nagapi2357-ui/Prime_Maxel-v3/research/Pythagorean_PWT_Connections.md

# Pythagorean Lost Secrets & Prime Wave Torsion — Research Note

**Author:** Nagaπ (with Adrian / Tusk Innovations)
**Date:** 5 March 2026
**Source Material:** Ken L. Wheeler, "Pythagoras Lost Secrets Recovered" (Feb 2026)
**Context:** Connections to Prime Wave Torsion (PWT) research and the Prime_Maxel-v3 circuit

---

## 1. Summary of Wheeler's Framework

Ken Wheeler presents a reconstruction of the ancient Pythagorean "Divided Line" (Plato's Republic 509d–511), arguing it encodes the complete structure of the cosmos through powers of Φ (phi, the golden ratio = 1.618033…).

### Core Claims

**The Divided Line as Universal Template:**
A single line, divided in harmonic ratio, then each section divided again identically, produces four segments corresponding to:

| Segment | Greek Letter | Element | Value | Meaning |
|---|---|---|---|---|
| Ι (Iota) | The One | Light/Principle | 1 | The Absolute |
| Θ (Theta) | Logos | Fire/Illumination | Φ | Beauty, harmony, the "holographic One" |
| Α (Alpha) | Animus | Air/Breath/Life | 1 (midpoint) | Living soul, breath of existence |
| Υ (Upsilon) | Water | — | 1 | Mediator |
| Γ (Gamma) | Gaia | Earth/Matter | 1/Φ | Phenomena, material world |

These spell ΥΓΙΘΑ (Ugieia) — the untranslatable Pythagorean greeting implying harmony, perfection, divine order, wholeness, beauty, and symmetry.

**The Circle is Φ³:**
- 360° = 137.5° + 137.5° + 85°
- 137.5° = the golden angle (Φ expressed in angular measure)
- 85° = 1 (the unit)
- 85 × Φ = 137.5
- 360 ÷ 85 = Φ³ = 4.23606…
- Therefore: a circle = Φ + Φ + 1 = Φ³

**The 108-36-36° Triangle:**
The isosceles triangle with apex 108° and base angles 36° is the only perfectly incommensurable geometry — self-similar at every scale. An "incommensurable cut" produces an identical smaller triangle. This is the geometry of the water molecule and the building block of the pentagram.

**Powers of Phi as Ontological Hierarchy:**

| Power | Value | Domain |
|---|---|---|
| Φ⁻³ | 0.23606 | ἀγνωσία — agnosis, the aoristos-dyad, ananke |
| Φ⁻² | 0.38196 | ψυχή — psyche, atman, citta, nous |
| 1/Φ | 0.61803 | Matter, phenomena |
| 1 | 1.0 | Being, the midpoint |
| Φ | 1.61803 | Beauty, logos, harmony |
| Φ² | 2.61803 | κόσμος νοητός — the metaphysical universe |
| Φ³ | 4.23606 | ALL — Pan, the entire universe |

**The Four Elements as Intermediates:**
The ancient diagram of Ignis–Aer–Aqua–Terra (Fire–Air–Water–Earth) with their qualities (Calidus/Frigida, Siccus/Humida, Subtilis/Corpulenta, Mobilis/Immobilis) maps onto the divided line, with "inmediate" relationships at ratios 8:12:18:27 — a geometric progression.

### The Ouroboros-Pentagram-Tree

The final image (slide 11) shows the serpent (ouroboros) encircling the pentagram inscribed over the tree of life — the Naga at the boundary, containing and bridging all realms.

---

## 2. The Royal Cubit Derivation

Adrian's independent derivation shows:

```
1 Royal Cubit = 0.5236m (established 1925, from pyramid measurements)

π / 6 = 0.52360…
π - Φ² = 3.14159… - 2.61803… = 0.52356…  ≈ 0.5236

Therefore: The Cubit ≈ π - Φ²
```

Additional note: 5 × 2 × 3 × 6 = 180 = π radians.

**Significance:** The ancient unit of measurement encodes the *difference* between transcendence (π, the irrational circle) and golden self-similarity (Φ²). The cubit is literally the gap between two fundamental constants — a bridge quantity.

---

## 3. Connections to Prime Number Theory

### 3.1 Φ and Primes — The Structural Bond

The Fibonacci sequence F(n), whose consecutive ratios converge to Φ, has deep prime entanglement:

- **Divisibility:** Every prime p divides some Fibonacci number. Specifically, p | F(p−1) or p | F(p+1) (depending on p mod 5).
- **Fibonacci primes:** F(n) is prime only if n is prime (necessary but not sufficient) — primality is a prerequisite for Fibonacci primality.
- **Lucas primality tests:** Lucas sequences (built on Φ) are the basis of the Lucas-Lehmer test for Mersenne primes, one of the most powerful primality tests known.
- **Zeckendorf's theorem:** Every positive integer has a unique representation as a sum of non-consecutive Fibonacci numbers — an alternative "base-Φ" decomposition paralleling prime factorisation.

Wheeler's framework suggests Φ is not merely a ratio but the *generative principle* of manifestation. If so, primes — as the irreducible atoms of arithmetic — would naturally emerge from Φ-structured processes.

### 3.2 The 108-36-36° Triangle and Self-Similar Prime Distribution

The incommensurable triangle's defining property is **fractal self-similarity**: subdivide it and the part is identical to the whole. Prime distribution exhibits analogous behaviour:

- **Scaling invariance:** The prime counting function π(x) ~ x/ln(x) shows that primes "thin out" logarithmically, but the *local* distribution at any scale resembles the global pattern — Cramér's model treats prime gaps as locally random with globally predictable statistics.
- **The Ulam spiral:** Primes plotted on a square spiral cluster along diagonal lines (quadratic polynomials). This is an empirical self-similarity — the pattern at small scale echoes at large scale.
- **Benford's law for primes:** The distribution of leading digits of primes follows logarithmic patterns reminiscent of golden-ratio scaling.

The 108-36-36° triangle may offer a geometric language for describing this: primes as the "incommensurable cuts" of the number line, each one producing a smaller copy of the overall distribution pattern.

### 3.3 The Golden Angle (137.5°) and Prime Spirals

The golden angle — 360° × (1 - 1/Φ) = 137.5077…° — is nature's optimal packing angle (sunflower seeds, phyllotaxis, sand dollars).

**Prime spiral hypothesis:** If primes are plotted on a spiral where each successive integer advances by the golden angle (rather than equal angular steps as in Ulam's spiral), do new patterns emerge? The golden angle's irrationality guarantees maximal separation between successive points, which could reveal prime clustering patterns invisible in Cartesian or equal-angle representations.

This connects directly to our PCB: the 12 Golden Cells at 30° spacing approximate a dodecagonal symmetry — but a golden-angle spacing (137.5° between successive cells) would create a phyllotactic arrangement, potentially more aligned with the theory.

### 3.4 Powers of Phi and Prime Gap Distribution

Wheeler's hierarchy (Φ⁻³ through Φ³) suggests discrete "levels" of manifestation. Prime gaps show a suggestive structure:

- The average gap near prime p is ~ln(p)
- The *distribution* of gap sizes follows patterns related to the Hardy-Littlewood conjectures
- **Observation:** The ratio of successive "record" prime gaps approximates Φ in certain ranges — e.g., the jump from gap 6 to gap 8 to gap 14 to gap 20 to gap 34… the Fibonacci-like growth pattern in maximal gaps has been noted by multiple researchers

If prime gaps grow in a Φ-scaled hierarchy, Wheeler's ontological levels would map to gap-size classes, with each "level" containing primes of a particular density character.

### 3.5 Five as the Generative Prime

Wheeler places 5 at the centre: Being = 5. In number theory, 5 is uniquely significant:

- **5 = Φ² + Φ⁻²** — the sum of golden powers
- **√5** appears in Binet's formula for Fibonacci numbers: F(n) = (Φⁿ - ψⁿ)/√5
- **5** is the hypotenuse-squared of the smallest Pythagorean triple (3² + 4² = 5²)
- **5** is the smallest prime that is a sum of two primes (2 + 3)
- **mod 5** determines Fibonacci divisibility by primes (via the Legendre symbol)
- The **pentagram** (5-pointed star) encodes Φ in every proportion
- **Fermat prime:** 5 = 2^(2¹) + 1, the second Fermat prime

In our circuit, the 12 cells × 5 signals per cell (TORSION_A, TORSION_B, VREF_MID, PULSE_IN, I2C) = 60 signal connections, and 60 = 5 × 12 = the number of edges in an icosahedron.

---

## 4. Dimensional Relationships

### 4.1 One-Dimensional: The Divided Line

The number line itself is Wheeler's Divided Line. Primes are the "uneven divisions" that create the harmonic structure:

- The fundamental theorem of arithmetic (unique prime factorisation) means every integer is a multiplicative "emanation" from primes — exactly Wheeler's claim that everything is a "multiplicative iteration of the One."
- The Sieve of Eratosthenes is literally the process of making successive cuts — each prime "divides" the line into harmonics.

### 4.2 Two-Dimensional: Spirals and Rings

**Ulam Spiral:** Primes on a square spiral → diagonal patterns (Hardy-Littlewood conjecture).

**Sacks Spiral:** Primes on an Archimedean spiral → parabolic curves.

**Golden Spiral:** Primes on a Φ-spiral → *unexplored territory*. The golden spiral's self-similar growth rate may resonate with the self-similar distribution of primes.

**Gaussian Primes:** In the complex plane Z[i], primes split into patterns governed by their residue mod 4:
- p ≡ 1 (mod 4) → splits into two Gaussian primes (e.g., 5 = (2+i)(2−i))
- p ≡ 3 (mod 4) → remains prime in Z[i]
- 2 = −i(1+i)² — the unique ramified prime

This 2D structure creates a lattice where prime distribution has *geometric* character — some primes are "larger" (unsplit) and others fragment into conjugate pairs, creating a torsion-like pairing.

**Our PCB's concentric rings** on B.Cu are a physical 2D prime-inspired geometry: TORSION_A (outer ring) and TORSION_B (inner ring) create paired concentric paths — a materialised Gaussian prime structure where signals flow in conjugate pairs.

### 4.3 Three-Dimensional: Zeta Landscape and Platonic Solids

**The Riemann Zeta Function |ζ(s)|:**
Plotted over the complex plane, the zeta function creates a 3D landscape of peaks and valleys. The non-trivial zeros — all conjectured to lie on the critical line Re(s) = ½ — are the "divided line" of analytic number theory. This ½ is Wheeler's midpoint (Alpha/Being), and the zeros encode the exact positions of primes.

**Platonic Solids and Phi:**
The icosahedron (20 triangular faces) and dodecahedron (12 pentagonal faces) are the only Platonic solids whose geometry is defined by Φ. Their vertices sit at coordinates involving (0, ±1, ±Φ) and permutations.

- The dodecahedron has **12 faces** — matching our 12 Golden Cells
- Each face is a **pentagon** — the Pythagorean ΥΓΙΘΑ symbol
- The dihedral angle of the dodecahedron is **116.565°** ≈ 360° - 2 × 137.5° (complement of two golden angles minus 360° ≈ 85° = Wheeler's "1")

**Quaternionic Primes (4D):**
In the Hurwitz quaternions, primes extend to 4 dimensions. The 24-cell polytope — unique to 4D and self-dual — governs the unit quaternions. It has 24 vertices, 96 edges, and 24 octahedral cells. Its structure intersects with the golden ratio through the 600-cell (which has icosahedral symmetry).

### 4.4 The Torsion Bridge as Dimensional Probe

Our circuit's TORSION_A and TORSION_B form a **differential pair** — mathematically, a 1D projection of a 2D phenomenon (the difference between two signals). By arranging 12 such pairs radially, we create:

- **1D:** Each differential measurement (TORSION_A − TORSION_B) per cell
- **2D:** The radial array of 12 measurements → angular distribution, like reading the "spiral" at 12 points
- **3D:** If cells are driven with phase-shifted excitations, the time dimension creates a helical (screw/torsion) pattern in signal space

This maps directly onto Wheeler's hierarchy: the One (total signal) → Logos (the differential) → Life (the dynamic/time-varying) → Water (the flowing/propagating) → Earth (the physical copper trace).

---

## 5. The Cubit as Torsion Constant

The Royal Cubit = π − Φ² deserves special attention.

In our context, "torsion" is the differential tension between two states. The cubit is precisely this — the *tension* between the two most fundamental mathematical constants:

- **π** = the circle, rotation, cycles, waves — the electromagnetic
- **Φ²** = self-similar growth, recursion, scaling — the structural/arithmetic

Their difference (0.5236) is small relative to either (~17% of π, ~20% of Φ²), suggesting the two principles are *almost* reconciled but not quite — there is a residual torsion. This residual is what the ancients encoded in their unit of measurement.

**Speculative connection:** If prime distribution is governed by the interplay of cyclic phenomena (the "music of the primes" in zeta function language) and self-similar scaling (the logarithmic thinning), then the "torsion" between these two principles — quantified by π − Φ² — may appear as a fundamental constant in prime gap statistics.

To test: examine whether π − Φ² (≈ 0.5236) or its reciprocal (≈ 1.9099) appears in the statistical distribution of normalized prime gaps.

---

## 6. The Naga Connection

The ouroboros serpent (slide 11) encircling the pentagram is the Naga — the bridge entity at the boundary between realms. In Adrian's mythology (Dusty's Road), Naga is "one of humanity's oldest words — found at water's edge on the deepest archaeological artefacts."

Wheeler places Water (Υ/Upsilon) as the mediator between Logos and Earth on the divided line. The Naga sits precisely here — at the water's edge, mediating between the intelligible and the sensible, between the abstract pattern (primes) and the physical measurement (circuit).

Our instrument is, in this framing, a Naga device: it sits at the interface between mathematical structure (the prime-inspired topology) and physical signal (the electromagnetic measurement), seeking to detect the torsion between worlds.

---

## 7. Open Questions for Future Investigation

1. **Golden-angle prime spiral:** Plot primes on a 137.5° spiral — do new clustering patterns emerge beyond Ulam/Sacks?
2. **Φ-scaled prime gaps:** Do maximal prime gaps grow as a Fibonacci-like sequence? Formalise the observation.
3. **π − Φ² in prime statistics:** Search for this constant in normalised prime gap distributions, twin prime ratios, or zeta zero spacings.
4. **Dodecahedral cell arrangement:** Would 12 cells at golden-angle spacing (rather than 30° equal spacing) produce different torsion signatures?
5. **5-fold signal symmetry:** The 5 signals per cell (TORSION_A/B, VREF, PULSE, I2C) — is there a natural pentagrammatic organisation of their relationships?
6. **Wildberger's maxel algebra:** Apply the maxel trend index framework (from the Symbiotic Futures project) to model prime-to-prime "ping" propagation through multiplicative structure.
7. **3D extension:** Design a follow-up board with cells arranged on a spherical or helical topology, probing 3D torsion.

---

## References

- Wheeler, K.L. (2026). "Pythagoras Lost Secrets Recovered." YouTube. https://youtu.be/AeIJzEDdEjI
- Plato, *Republic*, 509d–511e (The Divided Line)
- *Theology of Arithmetic* (attributed to Iamblichus)
- Timaeus, 31b–32c ("Two things alone cannot be satisfactorily united without a third")
- Wildberger, N.J. — Maxel algebra framework (rational trigonometry / algebraic number theory)
- Hardy, G.H. & Littlewood, J.E. — Conjectures on prime distributions
- Riemann, B. — "On the Number of Primes Less Than a Given Magnitude" (1859)

---

*"The (power of the) Divine's Illumination hath breathed life into the Waters & Firmament."*
*— ΥΓΙΘΑ, the Pythagorean greeting*
