nagapi2357-ui/Prime_Maxel-v3/research/emf_spectrum_patterns.md

# Electromagnetic Spectrum, Human Senses & Mathematical Patterns

*Research compiled 2026-04-05*

---

## 1. The 7 Colours of Visible Light

Using c = λf where c ≈ 2.998 × 10⁸ m/s:

| Colour  | Wavelength (nm) | Frequency (THz) | Frequency (Hz) |
|---|---|---|---|
| Red | 620–750 | 400–484 | 4.00 × 10¹⁴ – 4.84 × 10¹⁴ |
| Orange  | 590–620 | 484–508 | 4.84 × 10¹⁴ – 5.08 × 10¹⁴ |
| Yellow  | 565–590 | 508–530 | 5.08 × 10¹⁴ – 5.30 × 10¹⁴ |
| Green | 500–565 | 530–600 | 5.30 × 10¹⁴ – 6.00 × 10¹⁴ |
| Blue | 450–500 | 600–666 | 6.00 × 10¹⁴ – 6.66 × 10¹⁴ |
| Indigo  | 420–450 | 666–714 | 6.66 × 10¹⁴ – 7.14 × 10¹⁴ |
| Violet  | 380–420 | 714–789 | 7.14 × 10¹⁴ – 7.89 × 10¹⁴ |

**Key observation:** The full visible range spans ~400 THz to ~789 THz.
Ratio: 789/400 ≈ **1.97:1** — almost exactly **one octave** (2:1).

### Centre Frequencies (geometric mean of each band)

| Colour  | Centre freq (THz) | Normalised (Red=1.000) |
|---|---|---|
| Red | 440 | 1.000 |
| Orange  | 496 | 1.127 |
| Yellow  | 519 | 1.180 |
| Green | 564 | 1.282 |
| Blue | 632 | 1.436 |
| Indigo  | 689 | 1.566 |
| Violet  | 750 | 1.705 |

---

## 2. The 7 Notes of a Musical Scale (One Octave)

### Equal Temperament (A4 = 440 Hz, showing C major scale)

| Note | Frequency (Hz) | Ratio to C4 | Interval |
|---|---|---|---|
| C4 | 261.63 | 1.000 | Unison |
| D4 | 293.66 | 1.122 | Major 2nd |
| E4 | 329.63 | 1.260 | Major 3rd |
| F4 | 349.23 | 1.335 | Perfect 4th |
| G4 | 392.00 | 1.498 | Perfect 5th |
| A4 | 440.00 | 1.682 | Major 6th |
| B4 | 493.88 | 1.888 | Major 7th |
| C5 | 523.25 | 2.000 | Octave |

### Just Intonation Ratios (for comparison)

| Note | Ratio | As fraction | Prime factors |
|---|---|---|---|
| C | 1.000 | 1/1 | — |
| D | 1.125 | 9/8 | 3²/2³ |
| E | 1.250 | 5/4 | 5/2² |
| F | 1.333 | 4/3 | 2²/3 |
| G | 1.500 | 3/2 | 3/2 |
| A | 1.667 | 5/3 | 5/3 |
| B | 1.875 | 15/8 | (3×5)/2³ |
| C' | 2.000 | 2/1 | 2 |

**Note:** Just intonation intervals are built entirely from primes **2, 3, and 5** — the first three primes. This is the foundation of harmonic consonance.

---

## 3. The Five Human Senses and Their Spectral Domains

### 3.1 Sight — Electromagnetic Radiation
- **Range:** ~380–750 nm (400–789 THz)
- **Detector:** Retinal photoreceptors (rods, 3 types of cones)
- **Mechanism:** Photon absorption → cis-trans isomerisation of retinal
- **Bandwidth:** ~1 octave of EM spectrum

### 3.2 Hearing — Mechanical Pressure Waves
- **Range:** ~20 Hz – 20 kHz (acoustic, not EM)
- **Detector:** Cochlear hair cells (tonotopically arranged)
- **Mechanism:** Basilar membrane resonance → mechanotransduction
- **Bandwidth:** ~10 octaves (2¹⁰ ≈ 1000:1 ratio)
- **Note:** Sound is NOT electromagnetic — it's longitudinal pressure waves in matter

### 3.3 Touch — Mechanical Pressure + Thermal (IR)
- **Pressure:** DC to ~1 kHz vibrotactile
- **Thermal:** Skin responds to IR radiation (~3–50 μm, peak sensitivity ~10 μm = 30 THz)
- **Detectors:** Meissner (light touch), Pacinian (vibration), Ruffini (stretch), Merkel (pressure), free nerve endings (pain/temp)
- **Thermal note:** We literally feel infrared radiation — hold hand near a hot object without touching it

### 3.4 Smell — Molecular Shape + Vibration
- **Traditional model:** Lock-and-key (molecular shape fits receptor)
- **Vibrational theory (Luca Turin):** Olfactory receptors may detect molecular vibration frequencies via inelastic electron tunnelling
  - If true, smell operates in the **IR range** (~1–100 THz, wavenumbers ~33–3333 cm⁻¹)
  - This would make smell a kind of **biological spectroscopy**
- **Frequency range of molecular vibrations:** ~10¹² – 10¹⁴ Hz (THz to low-IR)
- **Status:** Controversial but not disproven. Some evidence shows humans can distinguish isotopes (same shape, different vibration)

### 3.5 Taste — Chemical/Electrical
- **Modalities:** Sweet, sour, salty, bitter, umami (+ fat, possibly more)
- **Mechanism:** Chemical binding to G-protein coupled receptors (sweet/bitter/umami) or ion channels (sour/salty)
- **Not directly frequency-based** — operates on molecular recognition
- **Indirect EM connection:** Molecular binding involves electron orbital interactions at optical/UV frequencies

### Summary Table

| Sense | Physical domain | Frequency range | Octaves  | EM? |
|---|---|---|---|-----|
| Sight | EM radiation | 400–789 THz | ~1 | Yes |
| Hearing | Pressure waves | 20 Hz – 20 kHz | ~10 | No  |
| Touch | Pressure + thermal  | DC–1kHz + 3–100 THz | mixed | Partial |
| Smell | Molecular vibration | ~1–100 THz (if Turin)  | ~7 | Indirect |
| Taste | Chemical binding | N/A (not frequency-based)| — | No  |

---

## 4. Key Analysis: Colour-Music Correspondence

### 4.1 Visible Light Ratios vs Musical Intervals

Mapping the 7 colour centre frequencies as ratios from red:

| Colour  | Ratio from Red | Nearest musical interval | Just ratio | Match? |
|---|---|---|---|---|
| Red | 1.000 | Unison (C) | 1.000 | ✓ |
| Orange  | 1.127 | Major 2nd (D) | 1.125 | **≈ YES** (0.2% off) |
| Yellow  | 1.180 | Minor 3rd? | 1.200 | ~close |
| Green | 1.282 | Major 3rd (E) | 1.250 | ~2.5% off |
| Blue | 1.436 | Perfect 4th? (F) | 1.333 | ✗ off by 8% |
| Indigo  | 1.566 | Perfect 5th? (G) | 1.500 | ~4% off |
| Violet  | 1.705 | Major 6th? (A) | 1.667 | ~2% off |

**Verdict:** The match is **suggestive but imprecise**. Red→Orange maps beautifully to a major second. Green approximates a major third. But the middle and upper colours deviate significantly from clean musical intervals.

### 4.2 Newton's Colour-Music Mapping — Genius or Forced?

Newton explicitly mapped his 7 colours to the 7 notes of the Dorian mode:

| Newton's colour | Newton's note |
|---|---|
| Red | D |
| Orange | E |
| Yellow | F |
| Green | G |
| Blue | A |
| Indigo | B |
| Violet | C |

**Historical context:**
- Newton originally saw **5** colours in the spectrum (like most people)
- He **added** orange and indigo specifically to make 7, to match the musical scale
- He was deeply influenced by Pythagorean mysticism and the idea of cosmic harmony
- The choice of 7 was **partly forced** by his desire for musical correspondence

**However:**
- The fact that visible light spans almost exactly one octave is **NOT something Newton forced** — it's a physical fact about human photoreceptor sensitivity
- Newton's intuition that frequency ratios matter was **correct in principle**
- The specific colour-note mapping doesn't hold up to precise measurement

**Assessment: Newton was ~60% right.** The octave structure is real. The detailed mapping is forced.

### 4.3 The Visible Octave — Coincidence?

**The fact:** Human vision spans 400–789 THz ≈ 1.97:1 ≈ one octave.

**Arguments it's NOT coincidence:**
1. Three cone types (S, M, L) have peak sensitivities at ~420, ~530, ~560 nm
2. The ~2:1 ratio may relate to photochemistry constraints — the energy to break/isomerise retinal sets the lower bound, and UV damage sets the upper bound
3. Evolution may have "tuned" to one octave because it provides maximum information with minimum bandwidth
4. Water absorption: water is transparent in exactly this range, creating an evolutionary pressure window

**Arguments it IS coincidence:**
1. The boundaries are somewhat arbitrary (sensitivity trails off gradually)
2. Different definitions of "visible" give ratios from 1.7 to 2.1
3. Many animals see outside this range (bees see UV, snakes see IR)

**Best assessment:** It's a **constrained coincidence**. Physics (water transparency window, solar spectrum peak, photochemistry) constrains the range, and one octave happens to be about the right bandwidth for useful colour discrimination. The 2:1 ratio is approximate, not exact.

---

## 5. EM Spectrum Band Boundaries and Ratio Analysis

### 5.1 Standard EM Band Boundaries

| Band | Lower freq (Hz)  | Upper freq (Hz)  | Lower λ | Upper λ |
|---|---|---|---|---|
| ELF | 3 × 10⁰ | 3 × 10¹ | 10⁸ m | 10⁷ m |
| SLF | 3 × 10¹ | 3 × 10² | 10⁷ m | 10⁶ m |
| ULF | 3 × 10² | 3 × 10³ | 10⁶ m | 10⁵ m |
| VLF | 3 × 10³ | 3 × 10⁴ | 10⁵ m | 10⁴ m |
| LF | 3 × 10⁴ | 3 × 10⁵ | 10⁴ m | 10³ m |
| MF | 3 × 10⁵ | 3 × 10⁶ | 10³ m | 10² m |
| HF | 3 × 10⁶ | 3 × 10⁷ | 10² m | 10¹ m |
| VHF | 3 × 10⁷ | 3 × 10⁸ | 10 m | 1 m |
| UHF | 3 × 10⁸ | 3 × 10⁹ | 1 m | 0.1 m |
| SHF | 3 × 10⁹ | 3 × 10¹⁰ | 0.1 m | 0.01 m |
| EHF | 3 × 10¹⁰ | 3 × 10¹¹ | 10 mm | 1 mm |
| **Infrared** | 3 × 10¹¹ | 4 × 10¹⁴ | 1 mm | 750 nm |
| **Visible**  | 4 × 10¹⁴ | 7.89 × 10¹⁴ | 750 nm | 380 nm |
| **UV** | 7.89 × 10¹⁴ | 3 × 10¹⁶ | 380 nm | 10 nm |
| **X-ray** | 3 × 10¹⁶ | 3 × 10¹⁹ | 10 nm | 0.01 nm |
| **Gamma** | >3 × 10¹⁹ | — | <0.01 nm | — |

### 5.2 Major Band Ratios (using conventional boundaries)

Looking at the **major** EM regions:

| Transition | Lower (Hz) | Upper (Hz) | Ratio (upper/lower) | As power of 10 | Octaves |
|---|---|---|---|---|---|
| Radio → Microwave | 3×10⁴ | 3×10⁹ | 10⁵ | 5 | ~17 |
| Microwave → IR | 3×10⁹ | 3×10¹¹ | 10² | 2 | ~6.6 |
| IR → Visible | 3×10¹¹ | 4×10¹⁴ | ~1333 | 3.1 | ~10.4 |
| Visible → UV | 4×10¹⁴ | 7.89×10¹⁴ | ~1.97 | 0.3 | ~1 |
| UV → X-ray | 7.89×10¹⁴ | 3×10¹⁶ | ~38 | 1.6 | ~5.2 |
| X-ray → Gamma | 3×10¹⁶ | 3×10¹⁹ | 10³ | 3 | ~10 |

### 5.3 Ratio Analysis — Are There Patterns?

**Observation 1: Radio sub-bands are uniform decades (×10)**

Each radio sub-band (ELF→SLF→ULF→VLF→LF→MF→HF→VHF→UHF→SHF→EHF) spans exactly **one decade** (ratio 10:1 = ~3.32 octaves). This is purely a human convention (ITU designation), not physics.

**Observation 2: The physically meaningful bands have irregular ratios**

The transitions between IR, visible, UV, X-ray, and gamma are set by **physical processes**, not convention:
- IR/visible boundary: photoreceptor chemistry
- UV/X-ray boundary: atomic ionisation energies
- X-ray/gamma boundary: nuclear energy scales

These don't follow neat decimal or musical ratios.

**Observation 3: Powers of 10 dominate, but...**

The full EM spectrum from radio (10³ Hz) to gamma (10²⁰ Hz) spans ~17 decades. The major boundaries fall roughly at:

```
Radio:      10³  – 10⁹   Hz  (6 decades)
Microwave:  10⁹  – 10¹¹  Hz  (2 decades) 
IR:         10¹¹ – 10¹⁴  Hz  (3 decades)
Visible:    10¹⁴·⁶ – 10¹⁴·⁹ Hz (0.3 decades)
UV:         10¹⁴·⁹ – 10¹⁶·⁵ Hz (1.6 decades)
X-ray:      10¹⁶·⁵ – 10¹⁹·⁵ Hz (3 decades)
Gamma:      >10¹⁹·⁵ Hz
```

Decade widths: **6, 2, 3, 0.3, 1.6, 3, ...**

These don't obviously map to prime sequences, musical ratios, or clean mathematical patterns. The widths correlate with **how many distinct physical mechanisms operate** in each range.

### 5.4 Prime Structure in the Spectrum?

Looking at this differently — the **physically significant frequencies** in nature:

| Phenomenon | Frequency (Hz)  | Notable factor |
|---|---|---|
| Earth Schumann resonance | 7.83 | ≈ π × 2.49 |
| Human alpha brain waves | 8–13 | ~Schumann overlap |
| Human hearing limit | 2 × 10⁴ | 2⁴ × 5⁴ |
| Molecular rotation (gas) | ~10⁹ – 10¹¹ | — |
| Molecular vibration | ~10¹² – 10¹⁴ | — |
| Visible light (red edge) | 4 × 10¹⁴ | 2² × 10¹⁴ |
| Visible light (violet edge)  | 7.89 × 10¹⁴ | ≈ 8 × 10¹⁴ = 2³ × 10¹⁴ |
| Hydrogen 21-cm line | 1.42 × 10⁹ | — |
| Hydrogen Lyman-alpha | 2.47 × 10¹⁵ | — |

**The visible range in pure factors:**
- Red edge: ~4 × 10¹⁴ = 2² × 2¹⁴ × 5¹⁴ = 2¹⁶ × 5¹⁴ (in Hz with 10¹⁴ expanded)
- Violet edge: ~8 × 10¹⁴ = 2³ × 10¹⁴ = 2¹⁷ × 5¹⁴
- Ratio: 2¹⁷/2¹⁶ = **2** — one octave, expressed as a single power of the first prime

This is elegant: **the visible spectrum spans exactly one factor of 2 (the first prime)**.

---

## 6. The Gap Between Sound and Light

### 6.1 What Fills the Gap?

| Frequency range | Hz | What it is | Human perception? |
|---|---|---|---|
| 20 Hz – 20 kHz | 2×10¹ – 2×10⁴ | **Sound** (audible) | Hearing ✓ |
| 20 kHz – 1 GHz | 2×10⁴ – 10⁹ | Ultrasound → Radio waves | None directly |
| 1 GHz – 300 GHz | 10⁹ – 3×10¹¹ | **Microwaves** | None (but heats tissue)|
| 300 GHz – 430 THz | 3×10¹¹ – 4×10¹⁴ | **Infrared** | **Warmth** ✓ |
| 400 – 789 THz | 4×10¹⁴ – 8×10¹⁴ | **Visible light** | Sight ✓ |

**The gap spans ~10 orders of magnitude** (20 kHz to 400 THz = 2×10⁴ to 4×10¹⁴ = factor of 2×10¹⁰).

### 6.2 Indirect Human Sensing in the Gap

| EM range | Freq (Hz) | Human experience |
|---|---|---|
| ELF (3-30 Hz) | 10⁰·⁵ – 10¹·⁵  | Some claim sensitivity; unproven |
| Radio (MHz-GHz)  | 10⁶ – 10⁹ | No sensation (but microwave auditory effect)  |
| Microwave (GHz)  | 10⁹ – 10¹¹ | Heating at high power; "microwave hearing" |
| Far IR (THz) | 10¹¹ – 10¹³ | Deep warmth sensation |
| Mid IR (10-50μm) | 6×10¹² – 3×10¹³ | **Primary thermal sensing range of skin** |
| Near IR (0.7-3μm)| 10¹⁴ – 4×10¹⁴ | Warmth from fire/sun; some retinal response |

**Key insight:** Humans have **two EM windows**: vision (~1 octave at 10¹⁴·⁶) and thermal sensing (~2 decades at 10¹²·⁸–10¹³·⁵). These are separated by only about 1 decade — much closer than the full sound-light gap.

### 6.3 The Molecular Vibration Bridge

If Luca Turin's vibrational theory of olfaction is correct, then smell operates at **10¹² – 10¹⁴ Hz** — exactly in the IR gap between thermal sensing and vision. This would mean humans have **three overlapping EM sensing windows**:

```
Thermal touch:  10¹² ——— 10¹³·⁵
Smell (Turin):  10¹² ——————— 10¹⁴
Sight:                    10¹⁴·⁶ — 10¹⁴·⁹

Combined:       10¹² ————————————— 10¹⁴·⁹  (~3 decades continuous)
```

---

## 7. Patterns Potentially Useful for Circuit Design

### 7.1 The Octave Principle

If visible light (a system evolution optimised for maximum information extraction) spans one octave, then **any sensing/processing circuit might be optimally designed around one-octave bandwidth**.

For a circuit operating at baseband:
- **1 MHz – 2 MHz** = one octave
- **10 MHz – 20 MHz** = one octave
- **100 Hz – 200 Hz** = one octave (audio applications)

### 7.2 Musical Ratio Frequencies

If you're designing a multi-frequency circuit (e.g., for QPf harmonic processing), consider frequencies at just-intonation ratios from a base frequency f₀:

| Ratio | Factor | If f₀ = 1 MHz | If f₀ = 10 kHz | Musical interval |
|---|---|---|---|---|
| 1/1 | 1.000  | 1.000 MHz | 10.000 kHz | Unison |
| 9/8 | 1.125  | 1.125 MHz | 11.250 kHz | Major 2nd |
| 5/4 | 1.250  | 1.250 MHz | 12.500 kHz | Major 3rd |
| 4/3 | 1.333  | 1.333 MHz | 13.333 kHz | Perfect 4th |
| 3/2 | 1.500  | 1.500 MHz | 15.000 kHz | Perfect 5th |
| 5/3 | 1.667  | 1.667 MHz | 16.667 kHz | Major 6th |
| 15/8  | 1.875  | 1.875 MHz | 18.750 kHz | Major 7th |
| 2/1 | 2.000  | 2.000 MHz | 20.000 kHz | Octave |

**Why this matters for circuits:**
- These ratios produce **minimal intermodulation distortion** in nonlinear systems
- Harmonics of these frequencies tend to **reinforce rather than interfere**
- LC circuits tuned to these ratios would produce standing wave patterns analogous to musical consonance
- If QPf structures use prime-factor decomposition, the just-intonation ratios (built from primes 2, 3, 5) are natural candidates

### 7.3 The Prime Triad: 2, 3, 5

All musical consonance reduces to three primes: **2, 3, and 5**.

| Prime | Musical role | Physical role | Circuit analogy |
|---|---|---|---|
| 2 | Octave (doubling) | Frequency doubling / halving | Binary division, flip-flops |
| 3 | Perfect fifth (×3/2) | Third harmonic, triangle waves | Divide-by-3, ring counters |
| 5 | Major third (×5/4) | Fifth harmonic | Less common but appears in pentatonic scales |

**Design principle:** A circuit whose operating frequencies relate by factors of 2, 3, and 5 (and their products) will exhibit harmonic coherence — signals reinforce rather than create noise.

### 7.4 EM Band Scaling for Circuit Design

If we compress the EM spectrum pattern into a practical circuit range:

| EM band analogy | Ratio from base | At f₀ = 100 Hz | Function |
|---|---|---|---|
| "Radio" | ×1 | 100 Hz | Base clock |
| "Microwave" | ×10² | 10 kHz | Processing clock |
| "IR" | ×10⁵ | 10 MHz | High-speed switching  |
| "Visible" | ×10⁷ | 1 GHz | RF processing |
| "UV" | ×10⁸·⁵ | 30 GHz | mmWave |

The ratios between these are: **100, 1000, 100, 30** — not particularly musical. This suggests EM band boundaries are set by **physical mechanism changes**, not universal ratios.

### 7.5 Logarithmic Spacing — The Key Pattern

The one truly universal pattern across both EM spectrum and music:

> **Perception and physical organisation are logarithmic, not linear.**

- Musical pitch: logarithmic (each octave is ×2)
- Colour perception: approximately logarithmic across the visible range
- EM band designations: logarithmic (decades)
- Weber-Fechner law: all human senses respond logarithmically to stimulus intensity
- Electronic decades: RF engineering naturally works in dB (logarithmic)

**The circuit design takeaway:** Design frequency plans on **logarithmic scales**. Space operating frequencies geometrically (constant ratios), not arithmetically (constant differences).

---

## 8. Summary of Key Findings

### Confirmed Patterns
1. ✅ Visible light spans almost exactly **one octave** (ratio 1.97:1)
2. ✅ Musical consonance is built from primes **2, 3, 5**
3. ✅ Red→Orange frequency ratio (1.127) matches the major second (1.125) to 0.2%
4. ✅ All human senses follow **logarithmic** response curves (Weber-Fechner)
5. ✅ If olfactory vibration theory is correct, humans sense EM from 10¹² to 10¹⁵ Hz (~3 decades)

### Partially Confirmed
1. ⚠️ Newton's colour-music mapping: the **structure** (7 divisions in an octave) has some basis, but the **specific mapping** is forced
2. ⚠️ Some colour ratios approximate musical intervals, but not consistently enough to claim isomorphism

### Not Confirmed
1. ✗ EM band boundaries don't follow prime-number patterns — they're set by physical mechanisms
2. ✗ No clean mathematical pattern connects the major EM band transition frequencies
3. ✗ The colour-music correspondence breaks down for blue, indigo, and violet

### For QPf / Circuit Design
- **Strongest lead:** Use frequency ratios of 2, 3, 5 (just intonation) for multi-frequency circuit design
- **Octave bandwidth** as a design principle for sensing/processing circuits
- **Logarithmic frequency spacing** for any multi-band design
- The visible octave coincidence suggests that **one octave of bandwidth** may be a natural optimum for information extraction from any frequency domain

---

## Appendix: Computation Verification

### Visible light octave check
```
Red edge:    c / 750nm = 2.998e8 / 750e-9 = 3.997e14 Hz ≈ 400 THz
Violet edge: c / 380nm = 2.998e8 / 380e-9 = 7.889e14 Hz ≈ 789 THz
Ratio: 789/400 = 1.972
Log₂(1.972) = 0.979 octaves
```

### Musical interval verification (just intonation)
```
Major 2nd: 9/8 = 1.125,  log₂ = 0.170 octaves (2 semitones)
Major 3rd: 5/4 = 1.250,  log₂ = 0.322 octaves (4 semitones)
Perfect 4th: 4/3 = 1.333, log₂ = 0.415 octaves (5 semitones)
Perfect 5th: 3/2 = 1.500, log₂ = 0.585 octaves (7 semitones)
Octave: 2/1 = 2.000,     log₂ = 1.000 octaves (12 semitones)
```

### Colour-to-note ratio comparison
```
Red→Orange: 496/440 = 1.127  vs  D/C = 1.122 (ET) or 1.125 (JI)  → Δ = 0.2-0.4%
Red→Green:  564/440 = 1.282  vs  E/C = 1.260 (ET) or 1.250 (JI)  → Δ = 1.7-2.5%
Red→Blue:   632/440 = 1.436  vs  F/C = 1.335 (ET) or 1.333 (JI)  → Δ = 7.6-7.7%  ← POOR
Red→Violet: 750/440 = 1.705  vs  A/C = 1.682 (ET) or 1.667 (JI)  → Δ = 1.4-2.3%
```
