nagapi2357-ui/Prime_Maxel-v3/research/great_pyramid_cubits/ANALYSIS.md

# The Great Pyramid of Giza — Dimensions in Royal Cubits

## Comprehensive Analysis

**Date:** 2026-03-05  
**Royal Cubit (RC):** 0.5236 m (7 palms × 4 fingers = 28 fingers)  
**Sources:** Petrie (1883), Cole (1925), Gantenbrink (1993), Lehner (1997), Edwards (1993), Wikipedia (compiled consensus)

---

## 1. External Dimensions

### 1.1 Base Side Lengths

The most authoritative survey is J.H. Cole (1925), Survey of Egypt Paper No. 39:

| Side  | Metres  | Royal Cubits | Deviation from 440 RC |
|---|---|---|---|
| North | 230.253 | 439.750 | −0.250 |
| East  | 230.391 | 440.013 | +0.013 |
| South | 230.454 | 440.134 | +0.134 |
| West  | 230.357 | 439.948 | −0.052 |
| **Mean** | **230.364** | **439.961** | **−0.039** |

**Petrie (1883):** Mean = 9068.8 inches = 230.348 m = 439.930 RC

**Design value: 440 RC** — confirmed by the near-perfect agreement of all surveys.

The max variation between sides is only 0.201 m (0.384 RC), demonstrating extraordinary precision for a 4,600-year-old structure.

**Implied cubit length:**
- From Cole mean: 230.364 / 440 = 0.52355 m
- From Petrie mean: 230.348 / 440 = 0.52352 m
- Standard value used: 0.5236 m

### 1.2 Height (Original with Pyramidion)

| Measurement | Metres | Royal Cubits |
|---|---|---|
| Design value | 146.608 | **280** |
| Petrie estimate | 146.710 | 280.196 |
| Current (without cap) | ~138.5 | ~264.5 |

**Design value: 280 RC** — derived from the seked of 5½ palms and the 440 RC base.

### 1.3 Slope Angle

The slope is defined by the **seked** (horizontal run per cubit of rise):
- Seked = 5½ palms = 5.5/7 cubits run per cubit rise
- **tan(θ) = 7/5.5 = 14/11**
- **θ = 51.8428° = 51°50'34"**
- Petrie measured: 51°50'40" (weighted mean of multiple methods)

### 1.4 Derived External Dimensions

| Dimension | Formula | Royal Cubits | Metres |
|---|---|---|---|
| **Half-base** | 440/2 | **220** | 115.192 |
| **Apothem** (slant height) | √(280² + 220²) = √126800 | **356.090** | 186.449 |
| **Edge** (corner to apex) | √(280² + (220√2)²) | **418.569** | 219.163 |
| **Perimeter** | 4 × 440 | **1760** | 921.536 |
| **Base diagonal** | 440√2 | **622.254** | 325.812 |
| **Base area** | 440² | **193,600** RC² | 53,077 m² |
| **Single face area** | ½ × 440 × 356.090 | **78,339.8** RC² | 21,477 m² |
| **Total lateral area** | 4 × face | **313,359** RC² | 85,910 m² |
| **Total surface area** | base + lateral | **506,959** RC² | 138,986 m² |

---

## 2. Internal Chambers and Passages

### 2.1 King's Chamber (Granite)

| Dimension | Metres | Royal Cubits | Likely Design |
|---|---|---|---|
| Length (E-W) | 10.470 | 19.996 | **20 RC** |
| Width (N-S) | 5.234 | 9.996 | **10 RC** |
| Height | 5.852 | 11.177 | **5√5 ≈ 11.180 RC** |
| Floor diagonal | — | 22.356 | **10√5 ≈ 22.361 RC** |

**Key finding:** If height = 5√5, then the **space diagonal = √(20² + 10² + (5√5)²) = √625 = 25 RC exactly**. This is almost certainly the design intent — Petrie's precise measurement (230.09" = 11.162 RC) is within 0.97 cm of 5√5 RC.

The King's Chamber is thus a **20 × 10 × 5√5** box with integer space diagonal 25.

### 2.2 Queen's Chamber (Limestone, gabled ceiling)

| Dimension | Metres | Royal Cubits | Likely Design |
|---|---|---|---|
| Length (E-W) | 5.75 | 10.98 | **~11 RC** |
| Width (N-S) | 5.23 | 9.99 | **10 RC** |
| Height to gable peak | 6.26 | 11.96 | **~12 RC** |
| Wall height (to gable spring) | ~4.67 | ~8.92 | **~9 RC** |

**Niche in east wall:**
- Height: 4.67 m = 8.92 RC
- Width at base: 1.57 m = 3.00 RC (5 steps, corbelled)
- Depth: 1.04 m = 1.99 RC ≈ **2 RC**

### 2.3 Grand Gallery

| Dimension | Metres | Royal Cubits | Likely Design |
|---|---|---|---|
| Length (along slope) | 46.68 | 89.15 | **~89 RC** |
| Floor width (between ramps) | 2.09 | 3.99 | **4 RC** |
| Height | 8.60 | 16.42 | **~16½ RC?** |
| Ramp bench width (each) | ~0.51 | ~0.97 | **~1 RC each** |
| Total width at base | ~3.43 | ~6.55 | **~6-7 RC** (with benches) |

Note: 89 is a **Fibonacci number** — possibly coincidental given measurement uncertainty.

### 2.4 Passages

| Passage | Length (slope) m | Length RC | Angle | tan(angle) |
|---|---|---|---|---|
| Ascending | 39.3 | 75.06 | 26°2'30" | 0.4886 ≈ ½ |
| Descending | 105.23 | 200.97 | 26°26'46" | 0.4974 ≈ ½ |

Both passages have slope angles corresponding to approximately **rise:run = 1:2** (tan ≈ 0.5).
- Cross-section: ~4 Egyptian feet (1.20 m) high × 2 cubits (1.05 m) wide

### 2.5 Subterranean Chamber (Unfinished, in bedrock)

| Dimension | Metres | Royal Cubits | Likely Design |
|---|---|---|---|
| Length (E-W) | 14.08 | 26.89 | **~27 RC** |
| Width (N-S) | 8.28 | 15.81 | **~16 RC** |
| Height | 3.18 | 6.07 | **~6 RC** |

---

## 3. Shaft Angles

Measured by Gantenbrink's Upuaut robotic survey (1993) and Petrie (1883):

| Shaft | Gantenbrink | Petrie | sin | cos | tan |
|---|---|---|-----|-----|-----|
| KC North | 32°36' | 31°33' | 0.539 | 0.842 | 0.640 |
| KC South | 45°00' | 44°26' | 0.707 | 0.707 | **1.000** |
| QC North | 39°07' | — | 0.631 | 0.776 | 0.813 |
| QC South | 39°36' | — | 0.638 | 0.770 | 0.828 |

**Notable:** KC South shaft at 45° has tan = 1, sin = cos = 1/√2.

**Proposed stellar alignments (c. 2500 BC):**
- KC South (~45°) → Orion's Belt (Al Nitak) meridian transit
- KC North (~32.5°) → Thuban (Alpha Draconis, then-pole star)
- QC South (~39.5°) → Sirius meridian transit
- QC North (~39°) → Kochab (Beta Ursae Minoris)

These are from Bauval & Gilbert (1994); contested by Krupp and others. The alignments depend sensitively on the assumed construction date and are not universally accepted.

---

## 4. Mathematical Relationships

### 4.1 π Relationships ★★★

| Relationship | Value | Target | Error |
|---|---|---|---|
| Perimeter / Height | 1760/280 = **44/7** = 6.28571... | 2π = 6.28319... | **0.040%** |
| Half-perimeter / Height | 880/280 = **22/7** | π = 3.14159... | **0.040%** |
| Base / Height | 440/280 = **11/7** | π/2 = 1.57080... | **0.040%** |

**This is the famous 22/7 approximation of π**, built into the design through the seked of 5½ palms. The ratio 14/11 (rise/run) gives 4 × base / height = 4 × (11/7) = 44/7 ≈ 2π.

**Classification: VERY CLOSE APPROXIMATION — likely inherent in the seked choice, possibly intentional.**

### 4.2 Φ (Golden Ratio) Relationships ★★★

| Relationship | Value | Target | Error |
|---|---|---|---|
| Apothem / Half-base | 356.09/220 = **1.61859** | Φ = 1.61803 | **0.034%** |
| Height / Half-base | 280/220 = **14/11** = 1.27273 | √Φ = 1.27202 | **0.056%** |
| Face area / (Half-base)² | **1.61859** | Φ = 1.61803 | **0.034%** |

**Critical insight:** These are NOT independent of the π relationship. For any pyramid where perimeter/height ≈ 2π:

sec(θ) = apothem/half-base = √(1 + tan²θ) where tan θ = 14/11

sec(arctan(4/π)) = √(1 + 16/π²) ≈ 1.6189 ≈ Φ

**The π and Φ relationships are mathematically coupled.** Choosing a seked that approximates π automatically approximates Φ. They are ONE relationship, not two.

### 4.3 √2, √3, √5 Relationships ★★

| Expression | Value (RC) | Notes |
|---|---|---|
| Base diagonal | 440√2 = 622.25 | By geometry |
| KC floor diagonal | √(20² + 10²) = **10√5** = 22.36 | Design intent |
| KC space diagonal | √(20² + 10² + (5√5)²) = **25** | **Integer!** |
| KC height | **5√5** ≈ 11.180 | Matches Petrie to 0.97 cm |

The King's Chamber appears designed so that its space diagonal is exactly **25 cubits** — a factor achieved by making height = 5√5.

### 4.4 Integer/Near-Integer Cubit Values ★★★

| Dimension | RC Value | Integer? |
|---|---|---|
| Base side | 440 | **YES** (design) |
| Height | 280 | **YES** (design) |
| Perimeter | 1760 | **YES** |
| Half-base | 220 | **YES** |
| KC Length | 20 | **YES** |
| KC Width | 10 | **YES** |
| KC Space Diagonal | 25 | **YES** (if h = 5√5) |
| QC Width | ~10 | **YES** |
| Grand Gallery width | ~4 | **YES** |
| Niche width (base) | ~3 | **YES** |
| Niche depth | ~2 | **YES** |

The Egyptians clearly designed in whole cubits wherever possible.

### 4.5 Prime Factorizations

| Value | Factorization | Primes involved |
|---|---|---|
| 440 | 2³ × 5 × 11 | 2, 5, 11 |
| 280 | 2³ × 5 × 7 | 2, 5, 7 |
| 1760 | 2⁵ × 5 × 11 | 2, 5, 11 |
| 220 | 2² × 5 × 11 | 2, 5, 11 |
| GCD(440,280) | 40 = 2³ × 5 | |
| Base/Height | 11/7 | Both prime! |

The fundamental ratio **11/7** involves two primes. The seked of 5½ = 11/2 palms per cubit rise encodes the ratio 14:11 (since 1 cubit = 7 palms).

### 4.6 The "Cubit Constant": π − Φ² ★★

```
π − Φ²  = 3.14159265... − 2.61803399... = 0.52355866...
RC      = 0.5236 m

Match:    0.5236 vs 0.5236  (to 4 decimal places)
Difference: 0.041 mm
```

This is a **remarkable numerical coincidence**. The Royal Cubit (based on forearm length, standardized across Egyptian history) happens to equal π − Φ² to 4 decimal places.

Since Φ² = Φ + 1, this is equivalently: **RC ≈ π − Φ − 1**

**Classification: NUMERICAL COINCIDENCE.** The cubit was an anthropometric unit. There is no mechanism by which forearm length would encode π − Φ². However, the coincidence is striking enough to be worth noting.

### 4.7 Pythagorean Relationships

The slope triangle (half-section) has sides 220, 280, and 356.09 RC.
- 220² + 280² = 126,800 = (√126800)² — **NOT a Pythagorean triple**
- Simplified: 11² + 14² = 317 (not a perfect square)

The King's Chamber: 20 × 10 floor gives diagonal 10√5.
- If height = 5√5: body diagonal = √(400 + 100 + 125) = √625 = **25** (Pythagorean!)
- The triple (20, 10, 5√5) with diagonal 25 is a valid 3D Pythagorean relationship

### 4.8 Passage Angles and 1:2 Slope

Both ascending and descending passages have tan(angle) ≈ 0.5:
- This corresponds to a **1:2 rise-to-run ratio** — the simplest non-trivial rational slope
- 26°26'46" is precisely arctan(1/2) = 26°33'54" → slight deviation suggests practical rather than exact targeting

---

## 5. The π − Φ² Recursion

### Do π and Φ reappear in ratios between cubit dimensions?

**YES — but this is tautological.** Since the external dimensions encode π (via 22/7), any ratio derived from them will contain π-related values:

| Ratio | Value | Mathematical constant |
|---|---|---|
| Base/Height | 11/7 ≈ π/2 | π/2 = 1.5708 |
| Height/Half-base | 14/11 ≈ √Φ | √Φ = 1.2720 |
| Apothem/Half-base | ≈ Φ | Φ = 1.6180 |
| Half-base/Edge | ≈ π/6 | π/6 = 0.5236 **(!)** |
| Height/Perimeter | ≈ 1/(2π) | 0.1592 |

**The ratio Half-base/Edge ≈ 0.5256 is close to π/6 = 0.5236 (0.38% error)** — and π/6 is itself close to the cubit constant π − Φ². So yes, the "recursion" appears, but it's a consequence of the single design choice (seked = 5½).

### Does the pyramid encode π/6 internally?

π/6 = 0.5236... ≈ π − Φ² ≈ RC in metres. The ratio half-base/edge approximates this, but with 0.38% error — larger than the 0.04% of the primary π relationship. This is likely a secondary coincidence rather than an intentional encoding.

---

## 6. Astronomical & Fringe Claims

### 6.1 Speed of Light Encoding — **DEBUNKED**

| Claim | Value |
|---|---|
| Pyramid latitude | 29.9792458° N |
| Speed of light | 299,792,458 m/s |

**Verdict: COINCIDENCE.**
- The metre was defined in 1791; Egyptians used cubits
- GPS precision to 7 decimal places was unavailable until the 1990s
- The pyramid base spans ~230 m; "the latitude" depends on which point you pick
- At ~30°N, the digits 2997... are constrained by geography

### 6.2 Earth Dimensions Encoding — **UNCONFIRMED**

| Claim | Calculation | Actual | Error |
|---|---|---|---|
| Height × 43,200 = Earth polar radius | 146.6 × 43,200 = 6,333,120 m | 6,356,752 m | **0.37%** |
| Perimeter × 43,200 = Earth circumference | 921.5 × 43,200 = 39,810,355 m | 40,075,017 m | **0.66%** |

**Verdict: INTERESTING BUT LIKELY COINCIDENCE.**
- The factor 43,200 is cherry-picked (= 2 × 360 × 60)
- Any ~150m tall structure at any slope would give some multiplier that "works"
- The ~0.4-0.7% errors are large compared to the pyramid's 0.04% construction precision
- However, the π relationship (perimeter ≈ 2π × height) IS built into the design

### 6.3 Stellar Shaft Alignments — **PLAUSIBLE BUT CONTESTED**

The Bauval-Gilbert hypothesis (1994) that the four shafts aimed at specific stars c. 2500 BC:
- Depends sensitively on the assumed epoch
- The shafts bend and vary in angle along their length
- Gantenbrink's precise measurements show the angles are not as clean as initially claimed
- Krupp (1997) and others have raised significant objections
- The QC shafts don't even reach the pyramid exterior

---

## 7. Summary of Mathematical Relationships

### Tier 1: Exact (By Design) ★★★
- Base = **440 RC**, Height = **280 RC** → integers
- Seked = **5½ palms** (ratio 14:11)
- King's Chamber = **20 × 10** RC (2:1 ratio)
- Passages at **~26°27'** (1:2 rise:run)

### Tier 2: Very Close Approximations (≤0.06% error) ★★★
- Perimeter/Height = **44/7 ≈ 2π** (0.040% error) — from seked choice
- Apothem/Half-base ≈ **Φ** (0.034% error) — mathematically coupled to π
- Height/Half-base ≈ **√Φ** (0.056% error) — same relationship

### Tier 3: Notable Coincidences ★★
- **π − Φ² = 0.5236 ≈ 1 Royal Cubit** (0.008% match!)
- KC space diagonal = **25 RC** (if height = 5√5)
- Grand Gallery length ≈ **89 RC** (Fibonacci number?)

### Tier 4: Fringe Claims ★
- Speed of light in latitude — coincidence
- Earth dimensions × 43,200 — cherry-picked multiplier
- Stellar shaft alignments — plausible but contested

---

## 8. The Deep Insight

The Great Pyramid's mathematical elegance flows from **one design choice**: the seked of 5½ palms, giving a rise:run ratio of **14:11**.

This single ratio simultaneously produces:
1. **π** — because 4 × 11/14 × 2 = 44/7 ≈ 2π
2. **Φ** — because sec(arctan(14/11)) ≈ Φ (this is a mathematical identity that holds for any angle where tan gives 4/π)
3. **Near-integer dimensions** — because 11 and 7 are small primes

The question of whether the Egyptians chose this seked *because* it encodes π, or whether they chose it for practical/aesthetic reasons and the π relationship is emergent, remains one of the most debated questions in Egyptology.

The Rhind Mathematical Papyrus (c. 1650 BC, copied from a c. 1850 BC original) shows the Egyptians used the approximation (16/9)² = 256/81 ≈ 3.1605 for the ratio of a circle's area to the square of its radius — suggesting they had a practical working knowledge of π without formalizing it. The 22/7 approximation embedded in the Great Pyramid is considerably more accurate than the Rhind Papyrus value.

---

---

## 9. The Perfect Number Connection

**1 Royal Cubit = 7 palms × 4 fingers = 28 fingers**

**28 is a perfect number** — it equals the sum of its proper divisors:
28 = 1 + 2 + 4 + 7 + 14

Only the second perfect number (after 6). They are extraordinarily rare — the next are 496 and 8128.

### Deep Connections

| Property | Value | Significance |
|---|---|---|
| 28 = 2² × 7 | Prime factorisation | 7 = palms per cubit |
| 28 = 2^(3−1) × (2³−1) | Euclid-Euler formula | Mersenne prime M₃ = 7 |
| 28 = T(7) = 1+2+3+4+5+6+7 | 7th triangular number | Sum of all parts = whole |
| Pyramid height = 280 = 10 × 28 | Design multiple | 10 perfect-number units |
| Perimeter = 1760 = 62.857 × 28 ≈ 20π × 28 | π recursion | π appears again through 28 |

### Pythagorean Significance

The Pythagoreans considered perfect numbers divine — they represent complete harmony, where the parts exactly reconstitute the whole. This is Wheeler's principle: the divisions of the One perfectly sum back to the One.

The choice of 28 fingers per cubit was almost certainly deliberate — the unit of measurement itself embodies "wholeness" before you even start building with it.

---

*Analysis by: pyramid_calculations.py (see companion script)*  
*All calculations reproducible via: `python3 pyramid_calculations.py`*
