nagapi2357-ui/Prime_Maxel-v3/JLCPCB/capture-2026-04-04T11_49_50.272Z.png

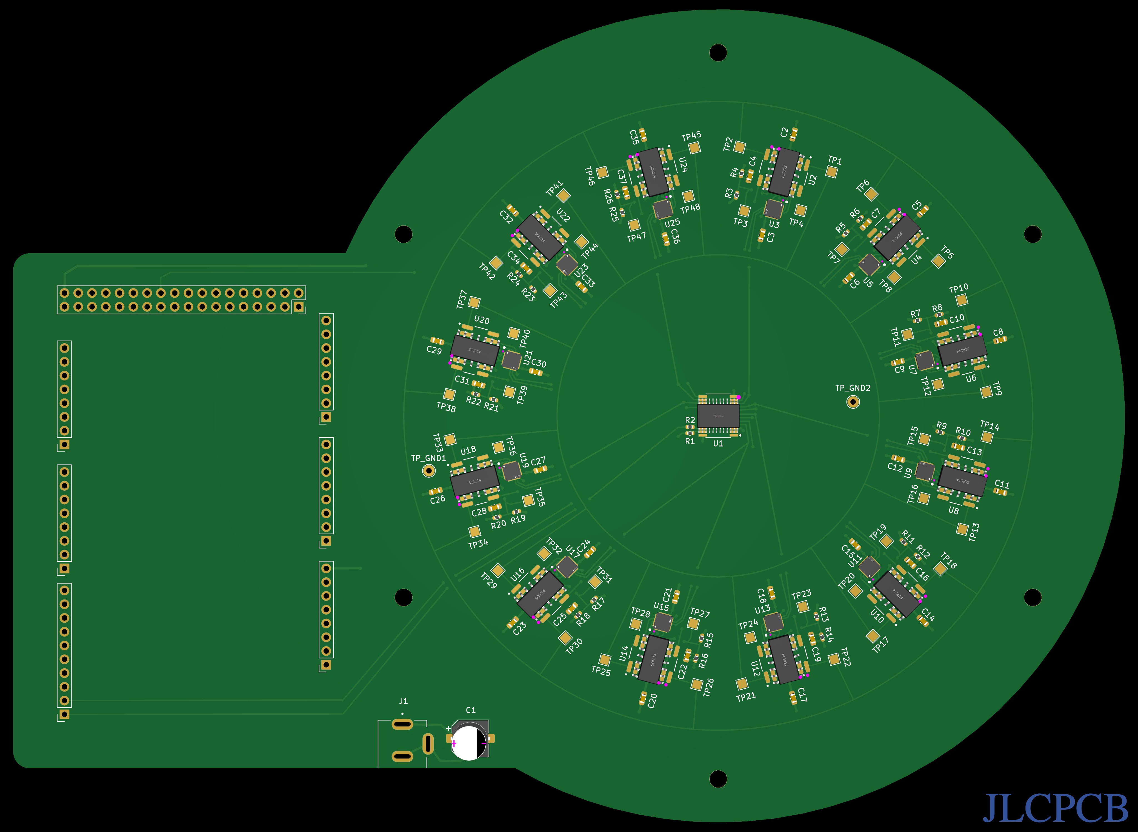
JLCPCB/capture-2026-04-04T11_49_50.272Z.png
