nagapi2357-ui/Prime_Maxel-v3/JLCPCB/Screenshot 2026-04-04 at 12.35.25.png

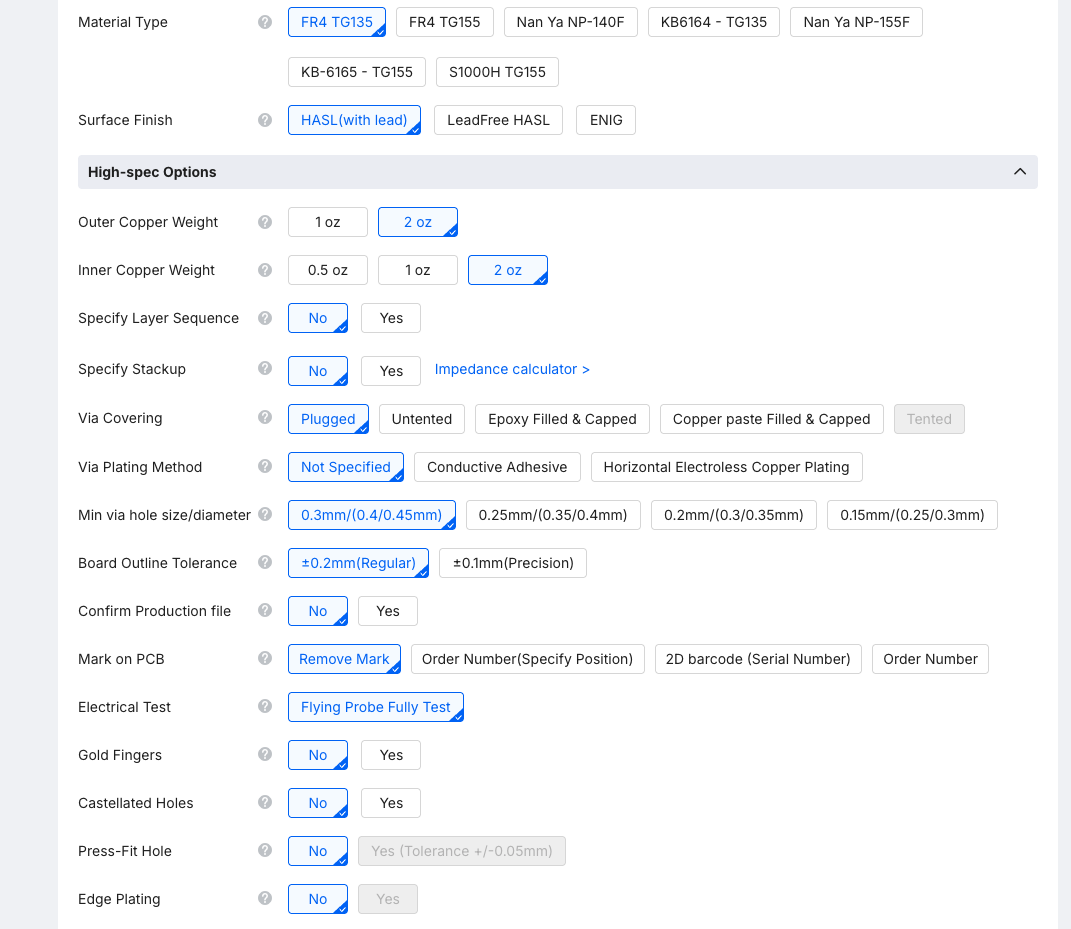
JLCPCB/Screenshot 2026-04-04 at 12.35.25.png
