nagapi2357-ui/Prime_Maxel-v3/LTspice_Sim/Files for Nagaπ from me/golden_cell_3ring - Kill the Pulse – V(ta1_in).png

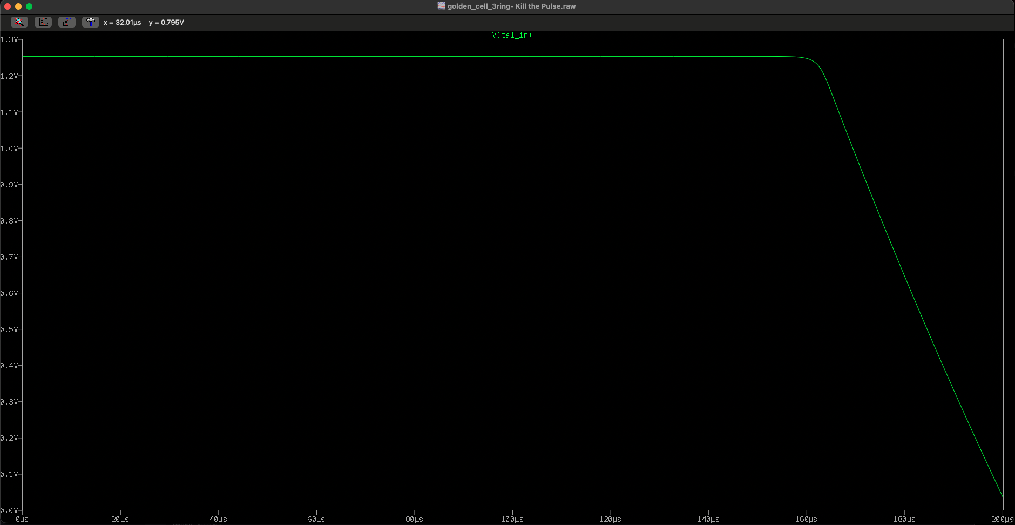
LTspice_Sim/Files for Nagaπ from me/golden_cell_3ring - Kill the Pulse – V(ta1_in).png
