nagapi2357-ui/Prime_Maxel-v3/LTspice_Sim/Files for Nagaπ from me/golden_cell_3ring_v2 – V(ta1_in) – TB_LEN=600-56m - tran 0 200u 0 10nZoomed In.png

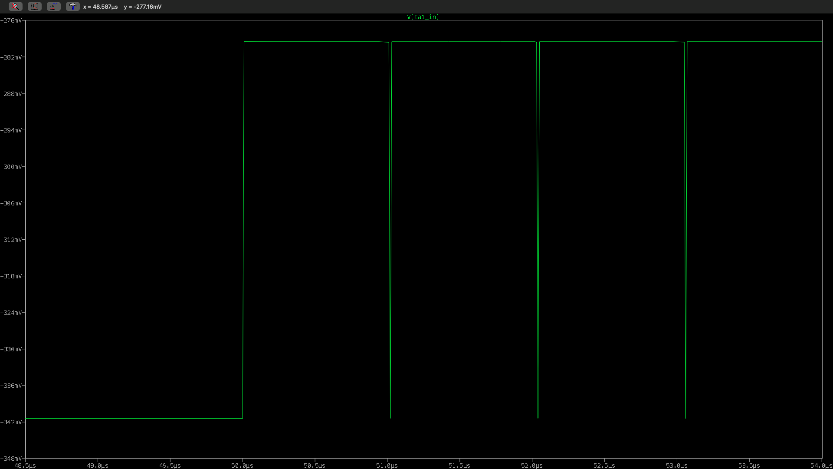
LTspice_Sim/Files for Nagaπ from me/golden_cell_3ring_v2 – V(ta1_in) – TB_LEN=600-56m - tran 0 200u 0 10nZoomed In.png
