nagapi2357-ui/Prime_Maxel-v3/LTspice_Sim/Files for Nagaπ from me/param TB_LEN=497-97m.png

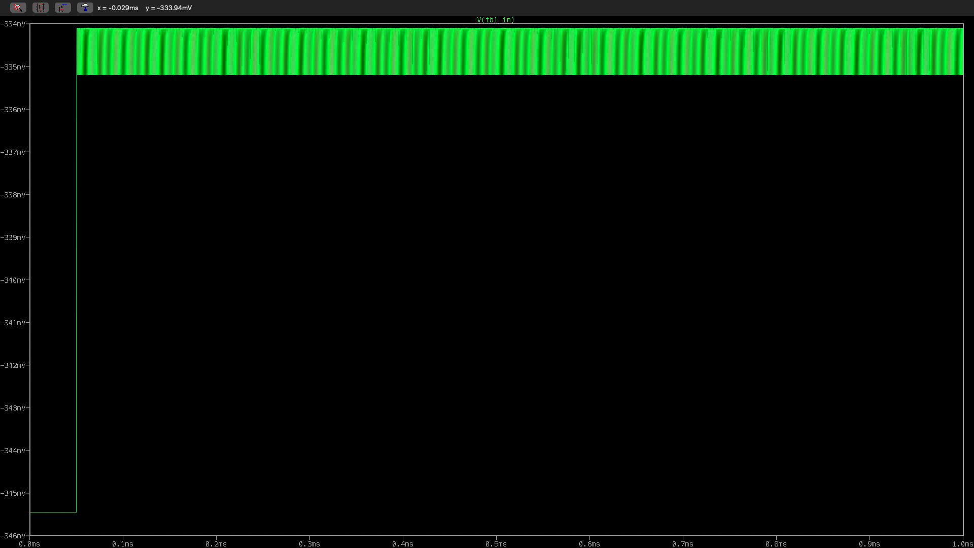
LTspice_Sim/Files for Nagaπ from me/param TB_LEN=497-97m.png
