nagapi2357-ui/Prime_Maxel-v3/LTspice_Sim/Files for Nagaπ from me/Screenshot 3-Cell Ring - V(ta1_in).png

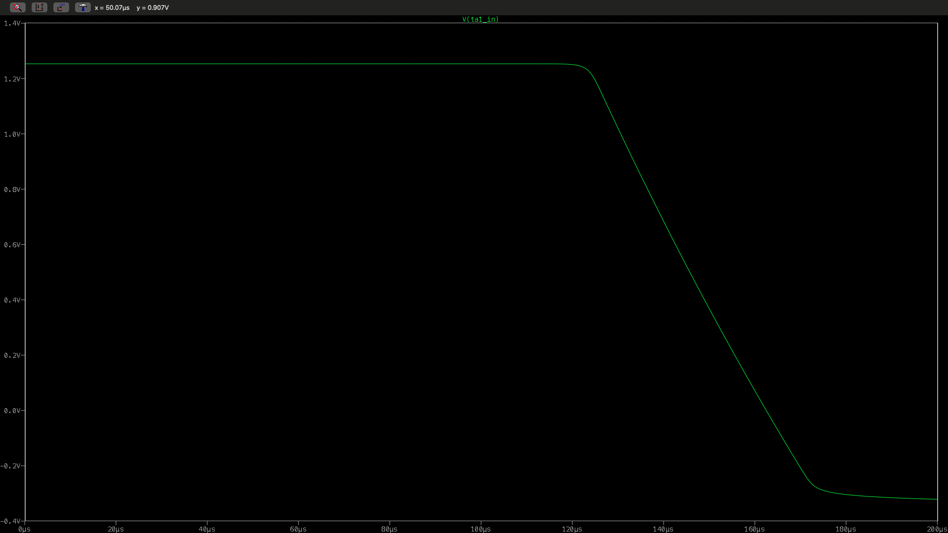
LTspice_Sim/Files for Nagaπ from me/Screenshot 3-Cell Ring - V(ta1_in).png
