nagapi2357-ui/Prime_Maxel-v3/LTspice_Sim/Files for Nagaπ from me/Screenshot 3-Cell Ring - V(tb1_in) V(tb2_in) V(tb3_in).png

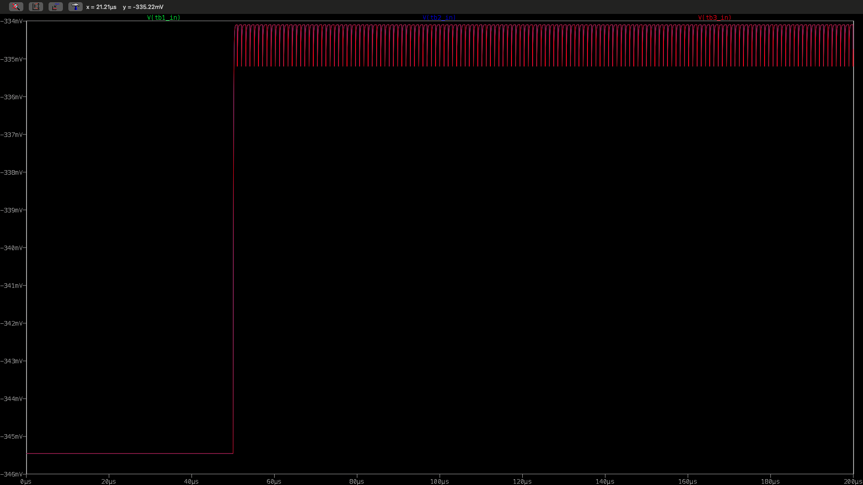
LTspice_Sim/Files for Nagaπ from me/Screenshot 3-Cell Ring - V(tb1_in) V(tb2_in) V(tb3_in).png
