nagapi2357-ui/Prime_Maxel-v3/LTspice_Sim/Files for Nagaπ from me/Screenshot golden_cell_3ring V(tb1_in)  Zoomed In 01.png

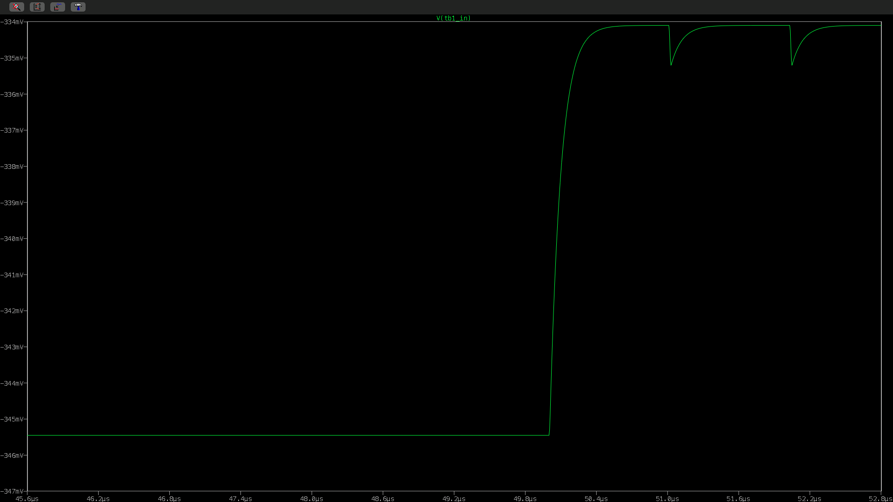
LTspice_Sim/Files for Nagaπ from me/Screenshot golden_cell_3ring V(tb1_in) Zoomed In 01.png
