nagapi2357-ui/Prime_Maxel-v3/LTspice_Sim/Files for Nagaπ from me/Screenshot Torsion Ratio Sweep - the 2-cell model.png

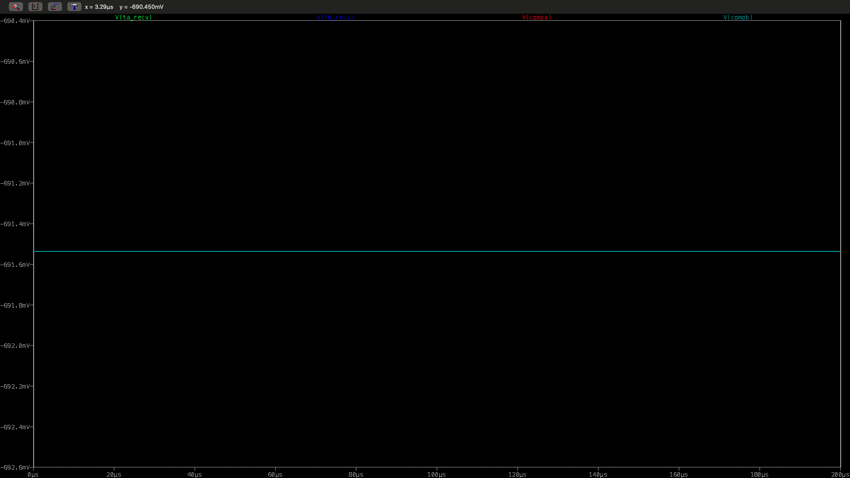
LTspice_Sim/Files for Nagaπ from me/Screenshot Torsion Ratio Sweep - the 2-cell model.png
