nagapi2357-ui/Prime_Maxel-v3/LTspice_Sim/Files for Nagaπ from me/X1 X10 SCOPE PROBE.webp

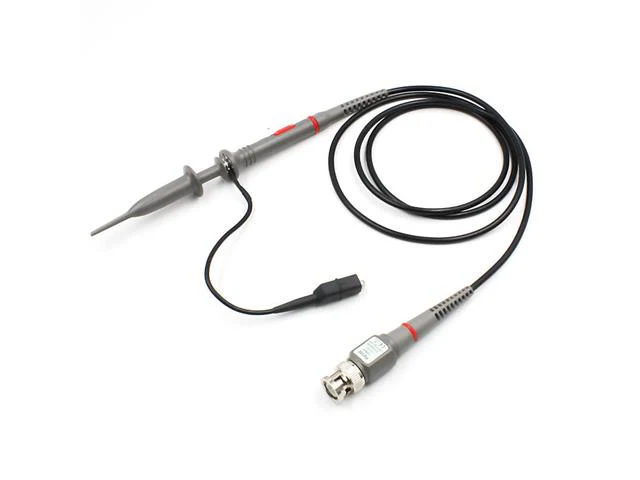
LTspice_Sim/Files for Nagaπ from me/X1 X10 SCOPE PROBE.webp
