nagapi2357-ui/Prime_Maxel-v3/research/conical_spiral_investigation/3_nn_log.png

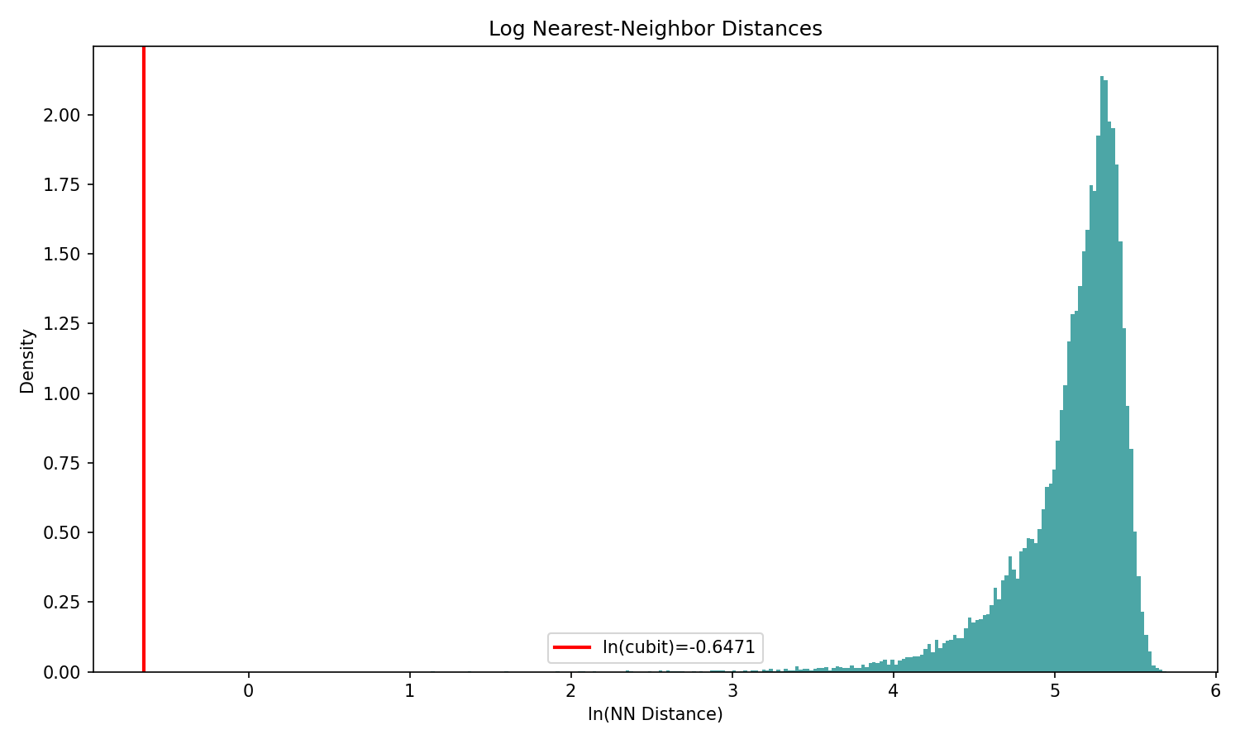
research/conical_spiral_investigation/3_nn_log.png
