nagapi2357-ui/Prime_Maxel-v3/research/conical_spiral_investigation/4_projections_logz.png

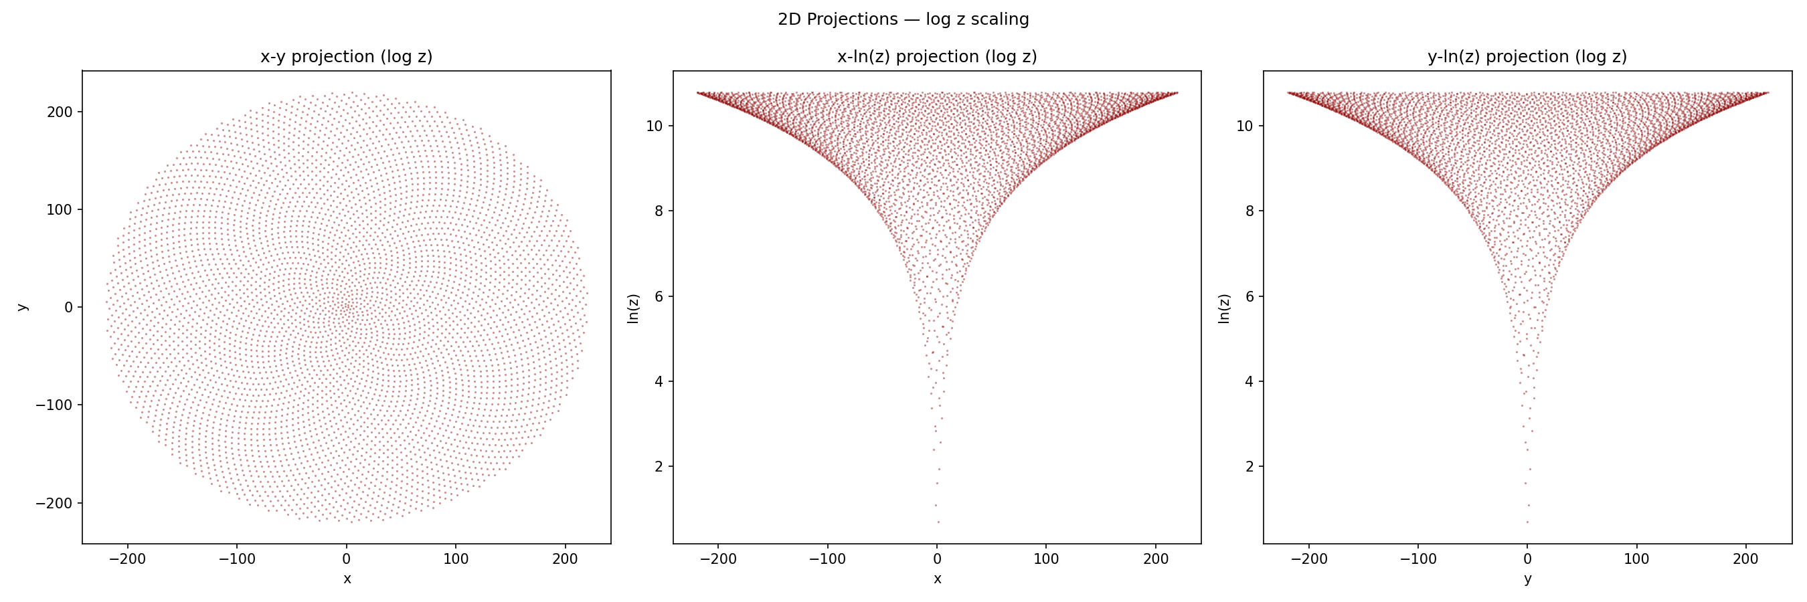
research/conical_spiral_investigation/4_projections_logz.png
